bigtreetech/smart-filament-detection-module/V2.0/Community Mods/Ender3 Max/SFS V2.0 Bracket for Ender3 Max -Pic(2).jpg

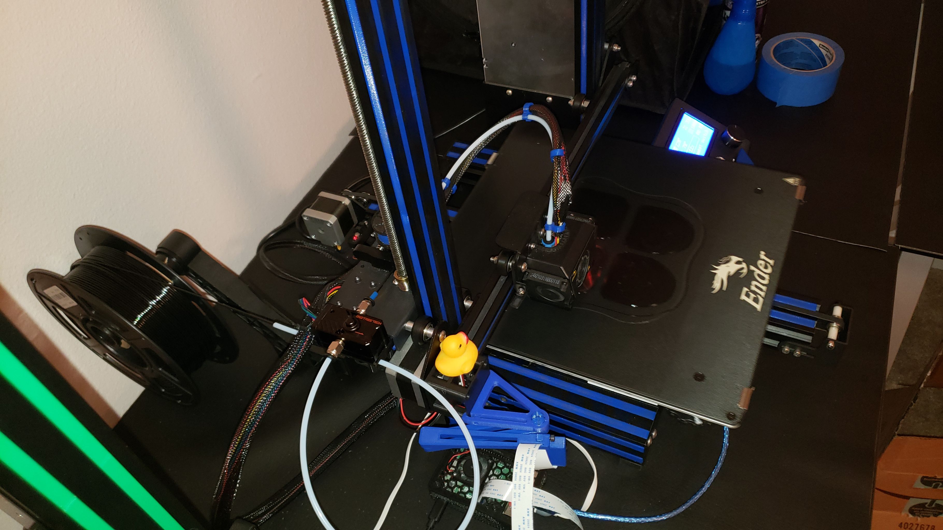
V2.0/Community Mods/Ender3 Max/SFS V2.0 Bracket for Ender3 Max -Pic(2).jpg
